arananet/SdMapperMSXJGILCAS/eagle/sdmapper-jgilcas.sch

## EAGLE design eagle/sdmapper-jgilcas.sch (2017-08-05)

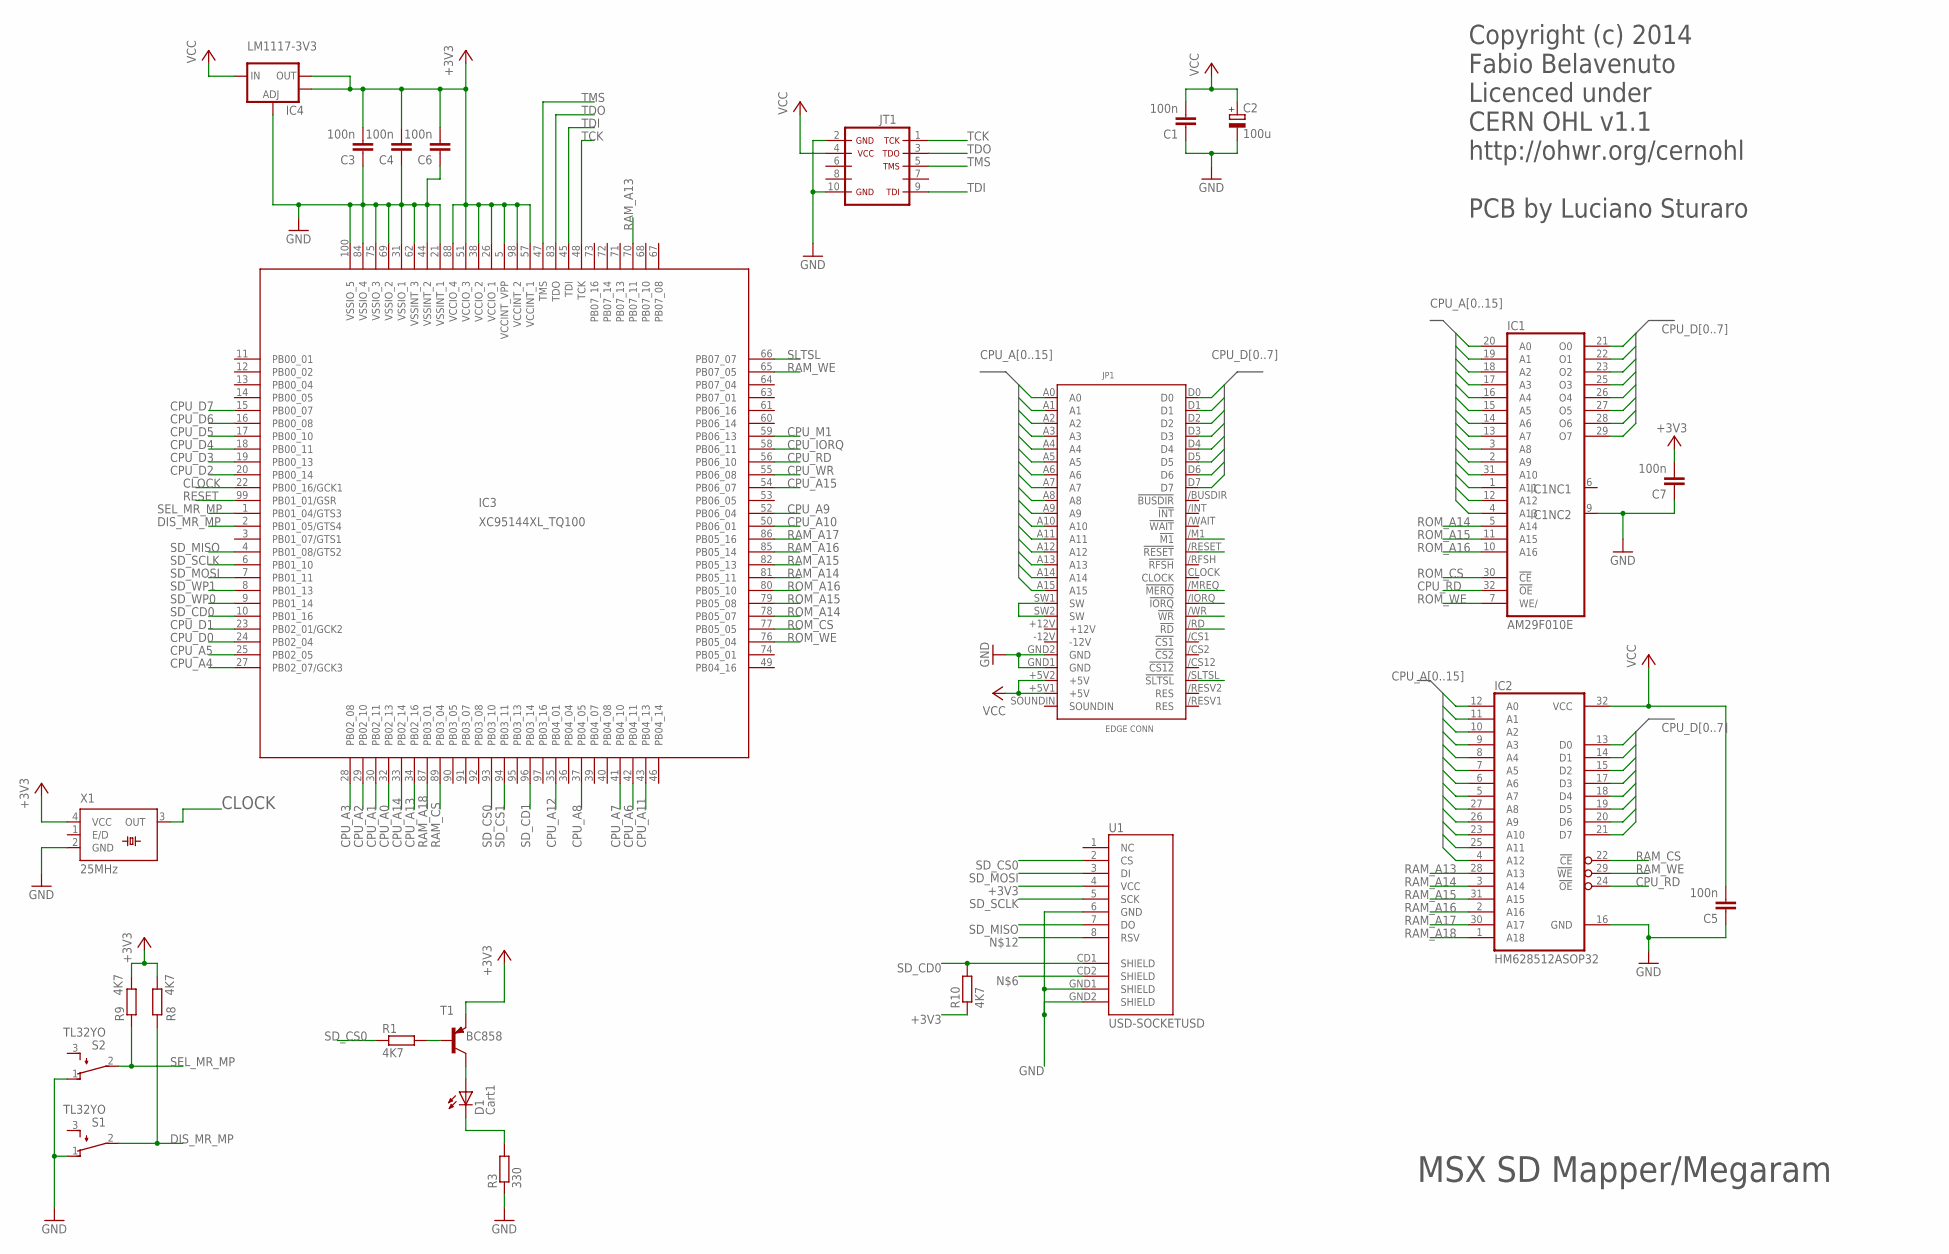
[picture p3: schematic sdmapper-jgilcas.sch]

Parts:
C1, C3, C4, C5: 100n; C0805
C2: 100u; SMC_B
C6, C7: 100n; C1206
D1: Cart1; CHIP-LED0805
IC1: AM29F010E; TSOP32
IC2: HM628512ASOP32; SOP32
IC3: XC95144XL_TQ100; XC-TQ100
IC4: LM1117-3V3; SOT223
JP1: MSXCART1; MSXCART
JT1: JTAG1A; PH5X2
R1, R8, R9, R10: 4K7; R0805
R3: 330; R0805
S1, S2: TL32YO; TL3XYO
T1: BC858; SOT23-BEC
U1: USD-SOCKETUSD; USD-SOCKET-PP
X1: 25MHz; SM77H

Connections:
+3V3: C3.2, C4.2, C6.2, C7.2, IC3.5 (VCCINT_VPP), IC3.26 (VCCIO_1), IC3.38 (VCCIO_2), IC3.51 (VCCIO_3), IC3.57 (VCCINT_1), IC3.88 (VCCIO_4), IC3.98 (VCCINT_2), IC4.2 (OUT), IC4.4 (OUT), R8.2, R9.2, R10.1, T1.E, U1.4 (VCC), X1.4 (VCC)
CLOCK: IC3.22 (PB00_16/GCK1), X1.3 (OUT)
CPU_A0: IC1.20 (A0), IC2.12 (A0), IC3.32 (PB02_13), JP1.A0
CPU_A1: IC1.19 (A1), IC2.11 (A1), IC3.30 (PB02_11), JP1.A1
CPU_A2: IC1.18 (A2), IC2.10 (A2), IC3.29 (PB02_10), JP1.A2
CPU_A3: IC1.17 (A3), IC2.9 (A3), IC3.28 (PB02_08), JP1.A3
CPU_A4: IC1.16 (A4), IC2.8 (A4), IC3.27 (PB02_07/GCK3), JP1.A4
CPU_A5: IC1.15 (A5), IC2.7 (A5), IC3.25 (PB02_05), JP1.A5
CPU_A6: IC1.14 (A6), IC2.6 (A6), IC3.42 (PB04_11), JP1.A6
CPU_A7: IC1.13 (A7), IC2.5 (A7), IC3.41 (PB04_10), JP1.A7
CPU_A8: IC1.3 (A8), IC2.27 (A8), IC3.37 (PB04_05), JP1.A8
CPU_A9: IC1.2 (A9), IC2.26 (A9), IC3.52 (PB06_04), JP1.A9
CPU_A10: IC1.31 (A10), IC2.23 (A10), IC3.50 (PB06_01), JP1.A10
CPU_A11: IC1.1 (A11), IC2.25 (A11), IC3.43 (PB04_13), JP1.A11
CPU_A12: IC1.12 (A12), IC2.4 (A12), IC3.35 (PB04_01), JP1.A12
CPU_A13: IC1.4 (A13), IC3.34 (PB02_16), JP1.A13
CPU_A14: IC3.33 (PB02_14), JP1.A14
CPU_A15: IC3.54 (PB06_07), JP1.A15
CPU_D0: IC1.21 (O0), IC2.13 (D0), IC3.24 (PB02_04), JP1.D0
CPU_D1: IC1.22 (O1), IC2.14 (D1), IC3.23 (PB02_01/GCK2), JP1.D1
CPU_D2: IC1.23 (O2), IC2.15 (D2), IC3.20 (PB00_14), JP1.D2
CPU_D3: IC1.25 (O3), IC2.17 (D3), IC3.19 (PB00_13), JP1.D3
CPU_D4: IC1.26 (O4), IC2.18 (D4), IC3.18 (PB00_11), JP1.D4
CPU_D5: IC1.27 (O5), IC2.19 (D5), IC3.17 (PB00_10), JP1.D5
CPU_D6: IC1.28 (O6), IC2.20 (D6), IC3.16 (PB00_08), JP1.D6
CPU_D7: IC1.29 (O7), IC2.21 (D7), IC3.15 (PB00_07), JP1.D7
CPU_IORQ: IC3.58 (PB06_11), JP1./IORQ (!IORQ)
CPU_M1: IC3.59 (PB06_13), JP1./M1 (!M1)
CPU_MREQ: JP1./MREQ (!MERQ)
CPU_RD: IC1.32 (!OE), IC2.24 (!OE), IC3.56 (PB06_10), JP1./RD (!RD)
CPU_WR: IC3.55 (PB06_08), JP1./WR (!WR)
DIS_MR_MP: IC3.2 (PB01_05/GTS4), R8.1, S1.2
GND: C1.1, C2.-, C3.1, C4.1, C5.1, C6.1, C7.1, IC1.9 (NC), IC2.16 (GND), IC3.21 (VSSINT_1), IC3.31 (VSSIO_1), IC3.44 (VSSINT_2), IC3.62 (VSSINT_3), IC3.69 (VSSIO_2), IC3.75 (VSSIO_3), IC3.84 (VSSIO_4), IC3.100 (VSSIO_5), IC4.1 (ADJ), JP1.GND1 (GND), JP1.GND2 (GND), JT1.2, JT1.10, R3.1, S1.1 (O), S2.1 (O), U1.6 (GND), U1.GND1 (SHIELD), U1.GND2 (SHIELD), X1.2 (GND)
unnamed: JP1.SW1 (SW), JP1.SW2 (SW)
unnamed: R1.2, T1.B
unnamed: D1.C, R3.2
unnamed: D1.A, T1.C
RAM_A13: IC2.28 (A13), IC3.70 (PB07_11)
RAM_A14: IC2.3 (A14), IC3.81 (PB05_11)
RAM_A15: IC2.31 (A15), IC3.82 (PB05_13)
RAM_A16: IC2.2 (A16), IC3.85 (PB05_14)
RAM_A17: IC2.30 (A17), IC3.86 (PB05_16)
RAM_A18: IC2.1 (A18), IC3.87 (PB03_01)
RAM_CS: IC2.22 (!CE), IC3.89 (PB03_04)
RAM_WE: IC2.29 (!WE), IC3.65 (PB07_05)
RESET: IC3.99 (PB01_01/GSR), JP1./RESET (!RESET)
ROM_A14: IC1.5 (A14), IC3.78 (PB05_07)
ROM_A15: IC1.11 (A15), IC3.79 (PB05_08)
ROM_A16: IC1.10 (A16), IC3.80 (PB05_10)
ROM_CS: IC1.30 (!CE), IC3.77 (PB05_05)
ROM_WE: IC1.7 (WE/), IC3.76 (PB05_04)
SD_CD0: IC3.10 (PB01_16), R10.2, U1.CD1 (SHIELD)
SD_CD1: IC3.96 (PB03_14)
SD_CS0: IC3.93 (PB03_10), R1.1, U1.2 (CS)
SD_CS1: IC3.94 (PB03_11)
SD_MISO: IC3.4 (PB01_08/GTS2), U1.7 (DO)
SD_MOSI: IC3.7 (PB01_11), U1.3 (DI)
SD_SCLK: IC3.6 (PB01_10), U1.5 (SCK)
SD_WP0: IC3.9 (PB01_14)
SD_WP1: IC3.8 (PB01_13)
SEL_MR_MP: IC3.1 (PB01_04/GTS3), R9.1, S2.2
SLTSL: IC3.66 (PB07_07), JP1./SLTSL (!SLTSL)
TCK: IC3.48 (TCK), JT1.1
TDI: IC3.45 (TDI), JT1.9
TDO: IC3.83 (TDO), JT1.3
TMS: IC3.47 (TMS), JT1.5
VCC: C1.2, C2.+, C5.2, IC2.32 (VCC), IC4.3 (IN), JP1.+5V1 (+5V), JP1.+5V2 (+5V), JT1.4

Notes on the sheet:
MSX SD Mapper/Megaram
Copyright (c) 2014 Fabio Belavenuto Licenced under CERN OHL v1.1 http://ohwr.org/cernohl PCB by Luciano Sturaro
